ChrisGuevara-Dev/bowlingPCB/img/Diag2_PCB.jpg

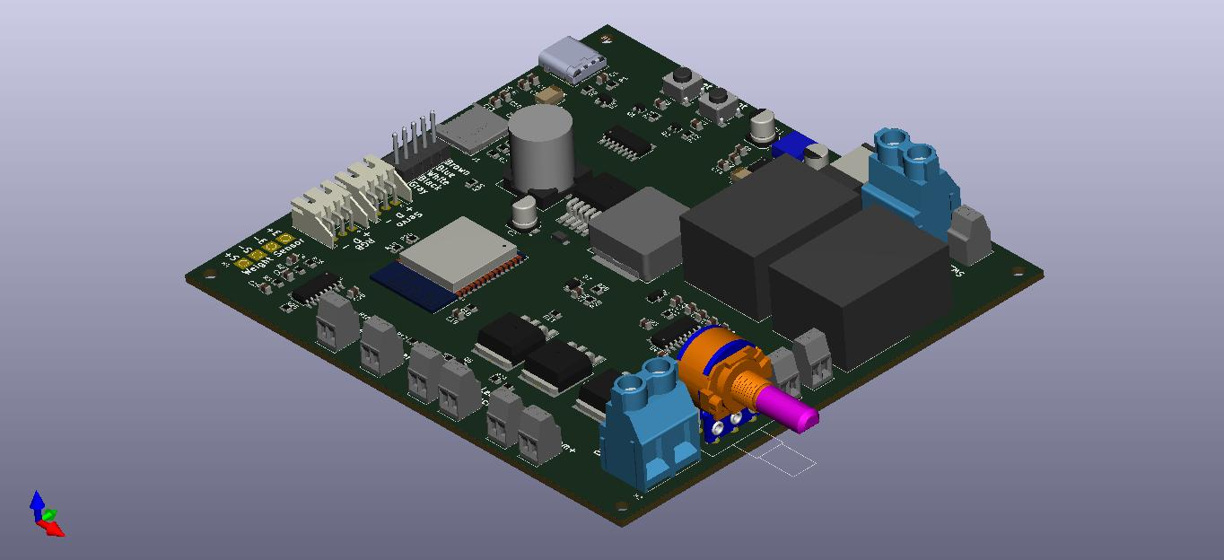
img/Diag2_PCB.jpg
