ChrisGuevara-Dev/bowlingPCB/img/Diag4_PCB.jpg

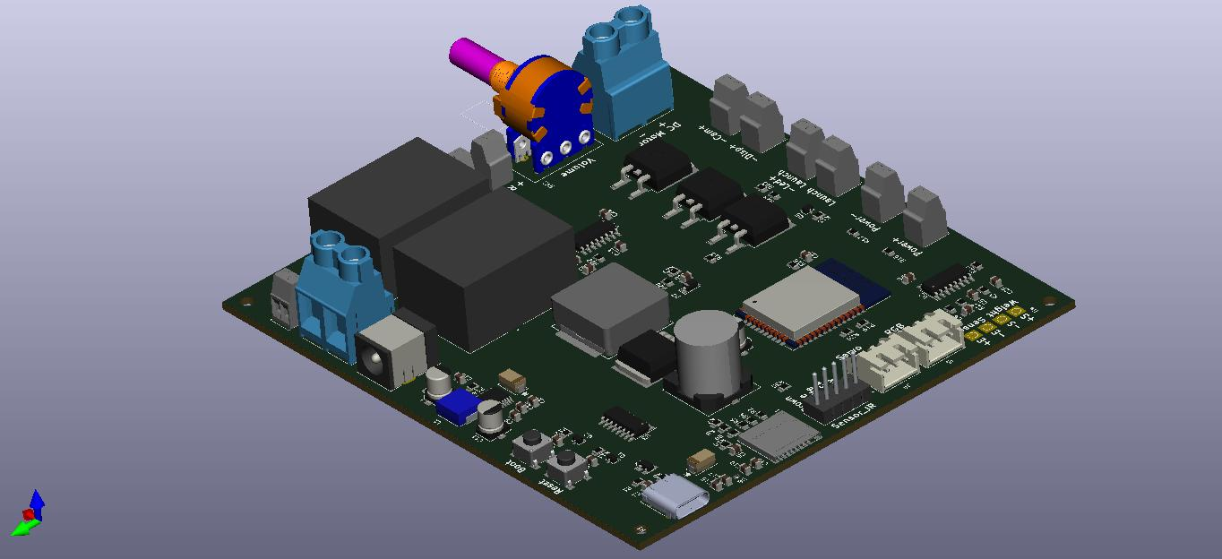
img/Diag4_PCB.jpg
