ChrisGuevara-Dev/bowlingPCB/img/L2_PCB.jpg

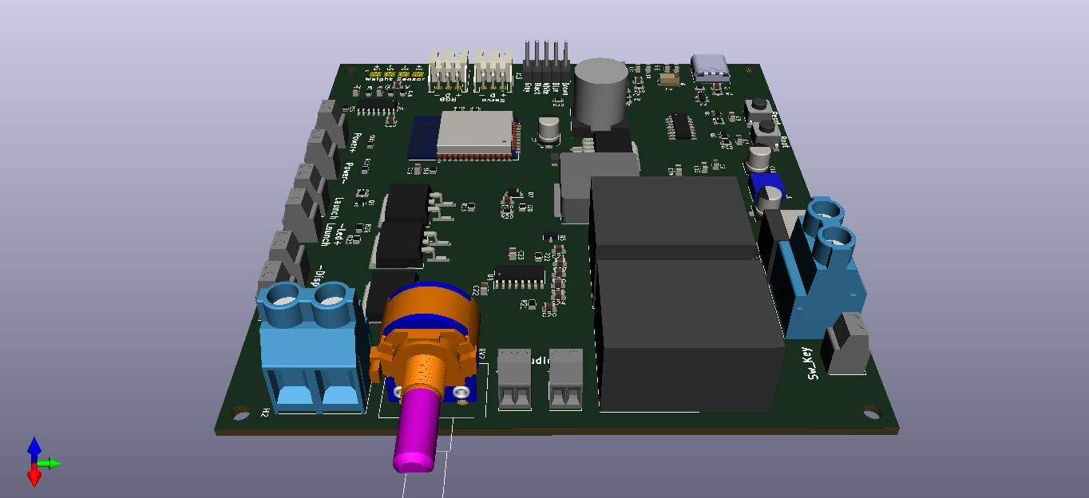
img/L2_PCB.jpg
