ChrisGuevara-Dev/bowlingPCB/img/L4_PCB.jpg

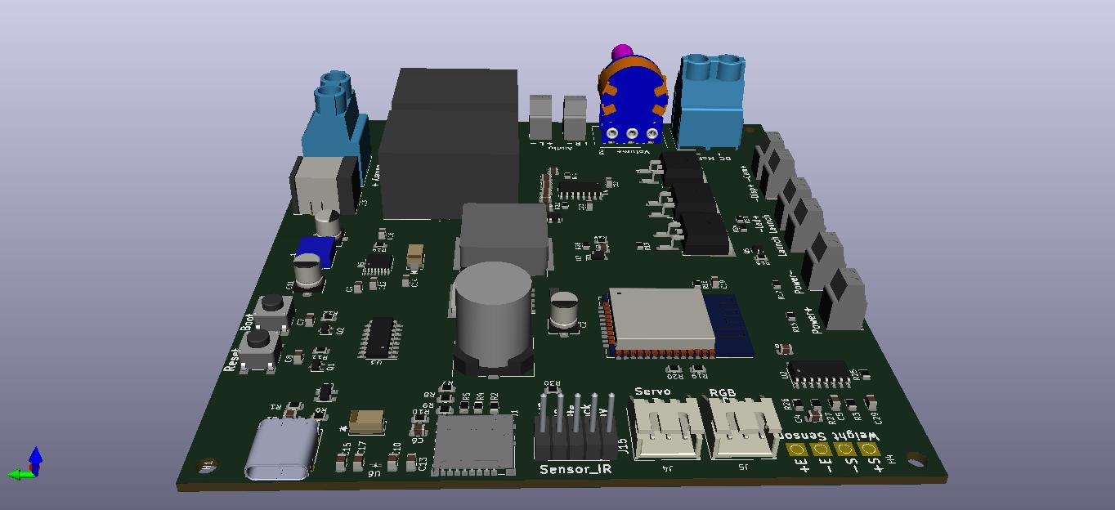
img/L4_PCB.jpg
