ChrisGuevara-Dev/bowlingPCB/img/PCB_page-0002.jpg

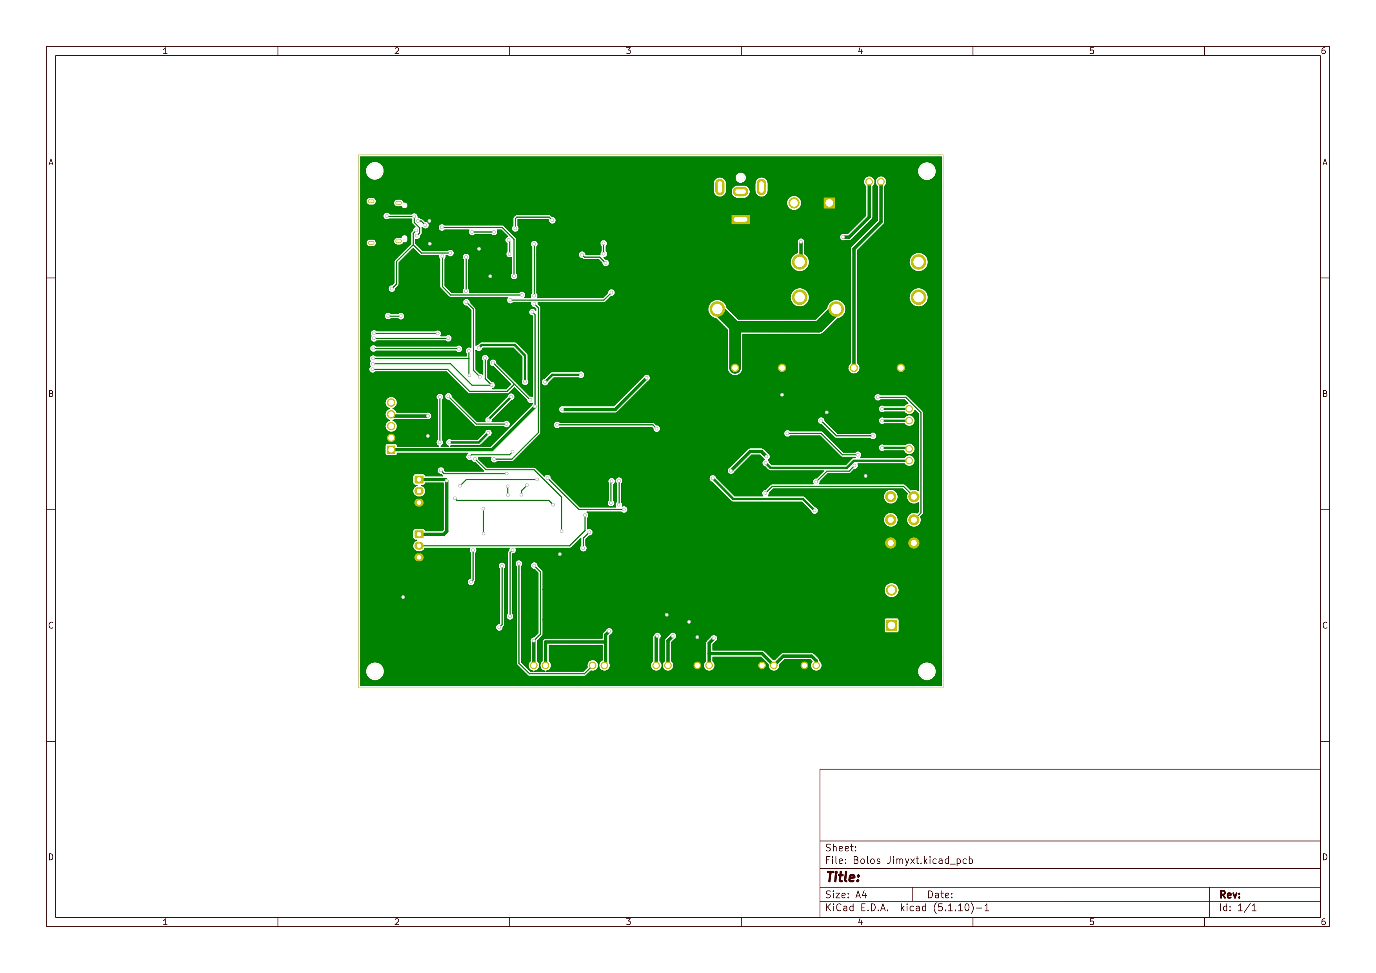
img/PCB_page-0002.jpg
