ChrisGuevara-Dev/bowlingPCB/img/PCB_page-0003.jpg

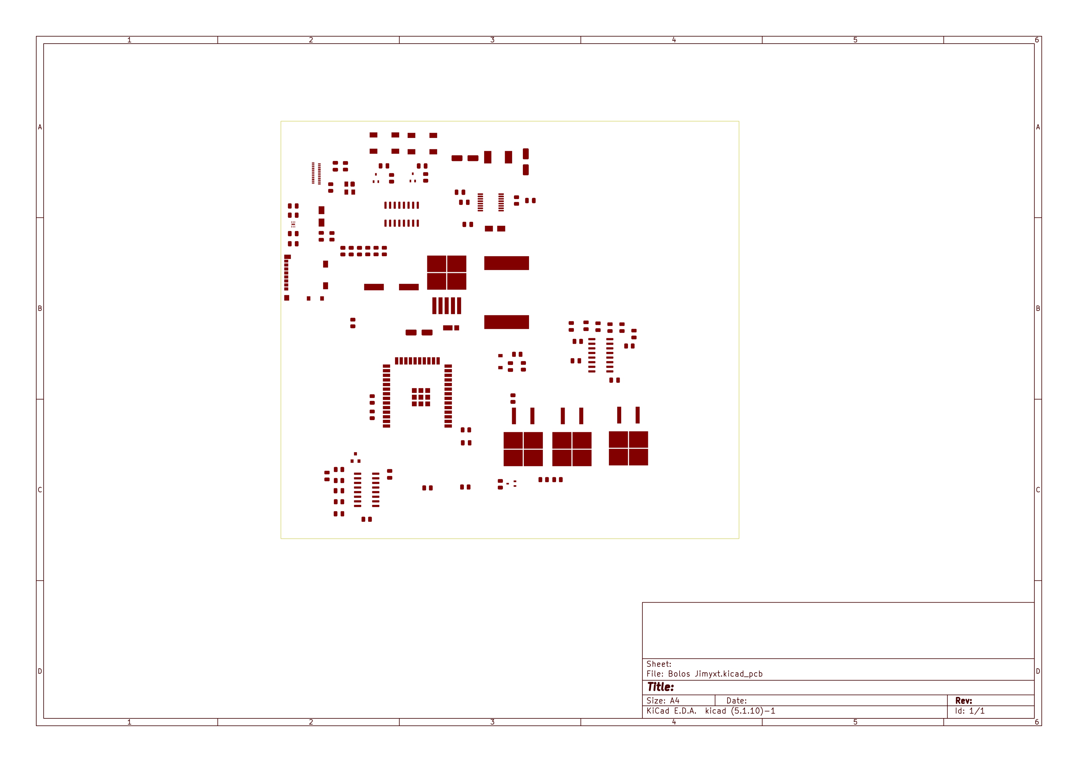
img/PCB_page-0003.jpg
