ChrisGuevara-Dev/bowlingPCB/img/PCB_page-0008.jpg

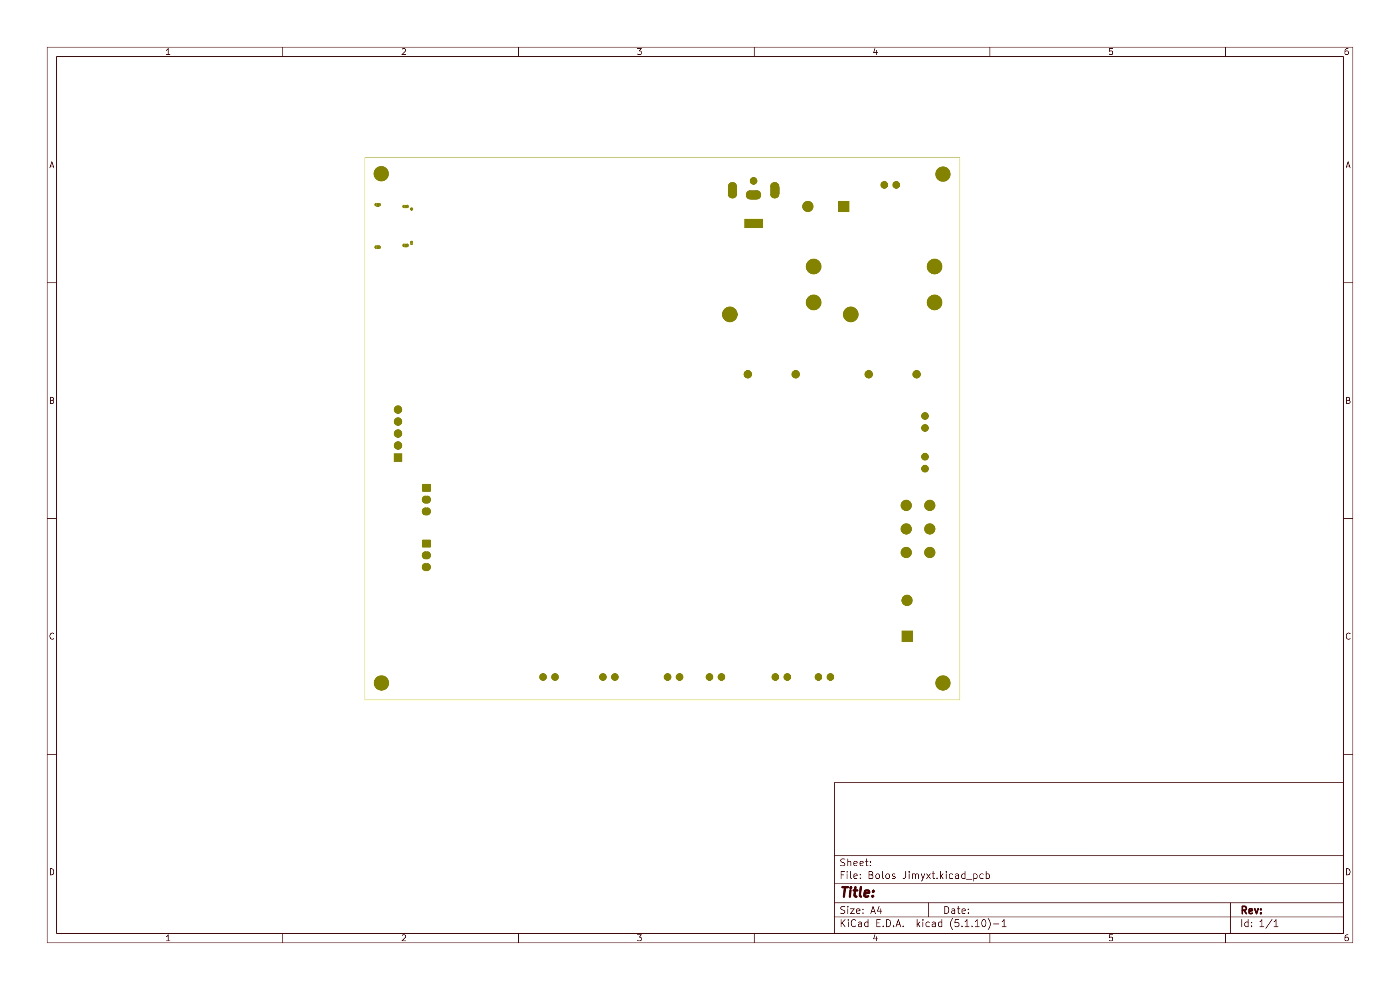
img/PCB_page-0008.jpg
